WaskaLabs/40VA-SINGLE-MOSFET-SSTC/MINI SSTC 1 PICS/ARCS AND SPARKS 6.5 INCH 1.jpg

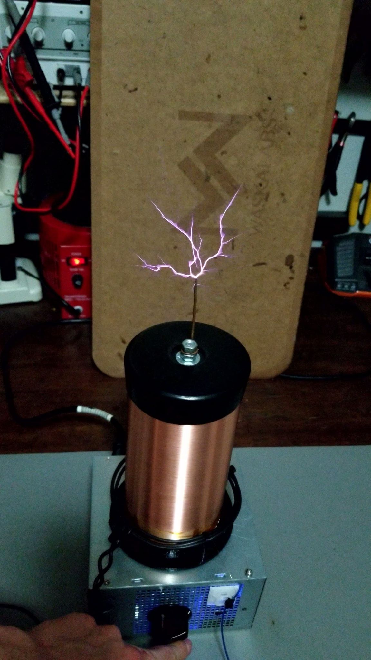
MINI SSTC 1 PICS/ARCS AND SPARKS 6.5 INCH 1.jpg
