WaskaLabs/40VA-SINGLE-MOSFET-SSTC/MINI SSTC 1 PICS/PCB PIC 1.jpg

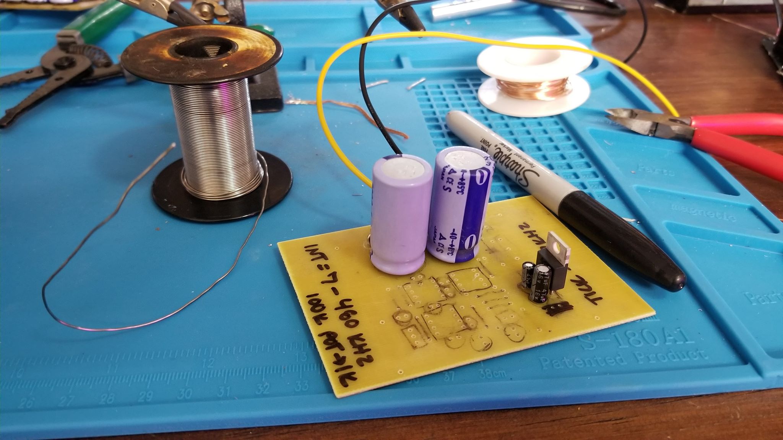
MINI SSTC 1 PICS/PCB PIC 1.jpg
