WaskaLabs/40VA-SINGLE-MOSFET-SSTC/V0 - MILLED VERSION/PCB & CONNECTIONS.png

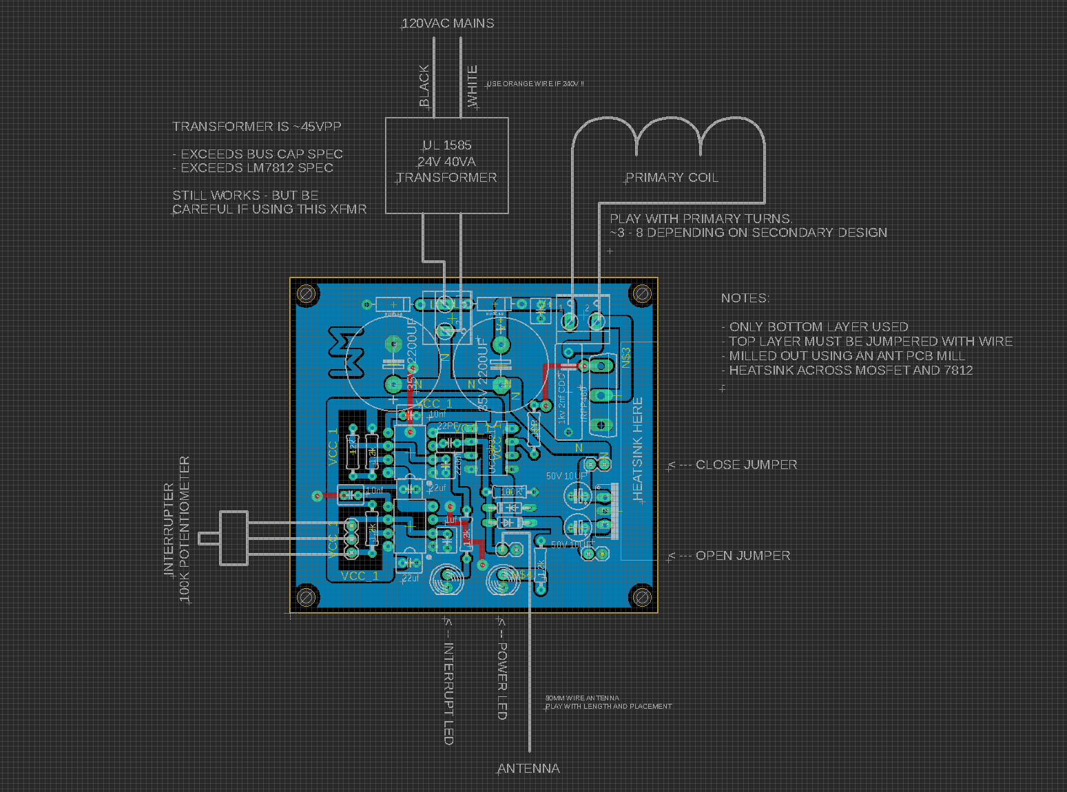
V0 - MILLED VERSION/PCB & CONNECTIONS.png
