WaskaLabs/40VA-SINGLE-MOSFET-SSTC/MINI SSTC 1 PICS/3D PRINTED COIL HOLDER.jpg

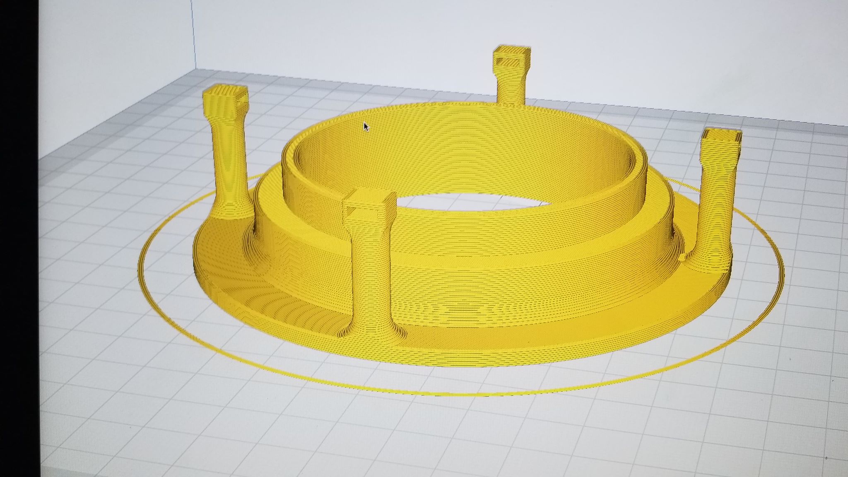
MINI SSTC 1 PICS/3D PRINTED COIL HOLDER.jpg
