WaskaLabs/40VA-SINGLE-MOSFET-SSTC/MINI SSTC 1 PICS/FINAL ASSEMBLY 4.jpg

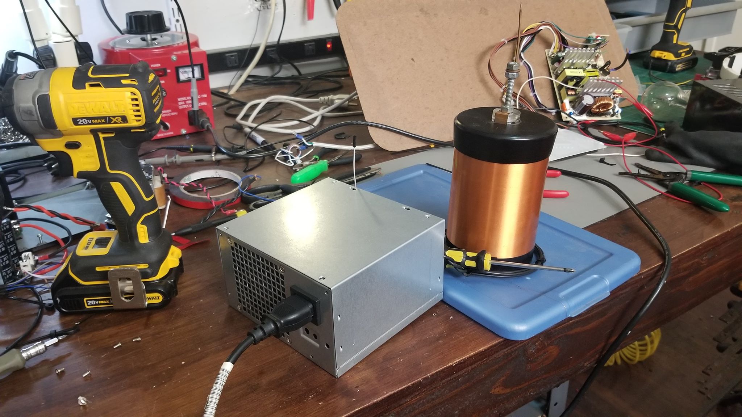
MINI SSTC 1 PICS/FINAL ASSEMBLY 4.jpg
