WaskaLabs/40VA-SINGLE-MOSFET-SSTC/MINI SSTC 1 PICS/FINAL ASSEMBLY 5.jpg

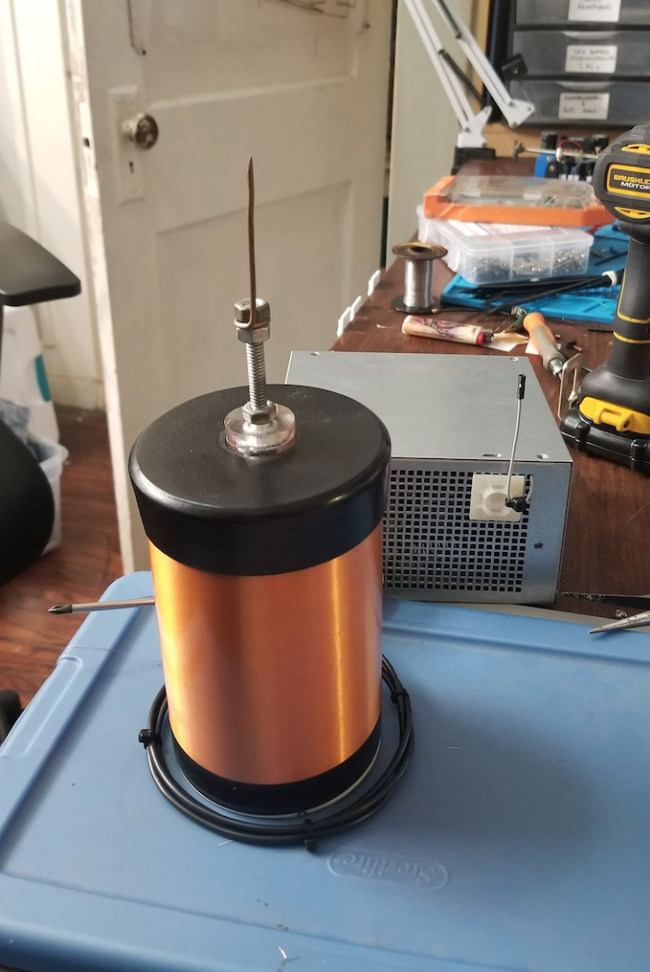
MINI SSTC 1 PICS/FINAL ASSEMBLY 5.jpg
