WaskaLabs/40VA-SINGLE-MOSFET-SSTC/MINI SSTC 1 PICS/FINAL ASSEMBLY GUTS.jpg

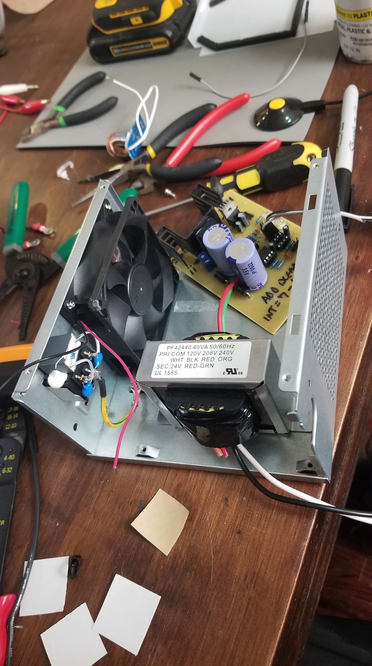
MINI SSTC 1 PICS/FINAL ASSEMBLY GUTS.jpg
