WaskaLabs/40VA-SINGLE-MOSFET-SSTC/MINI SSTC 1 PICS/FIRST PCB TESTS WITH 555 INTERRUPT.jpg

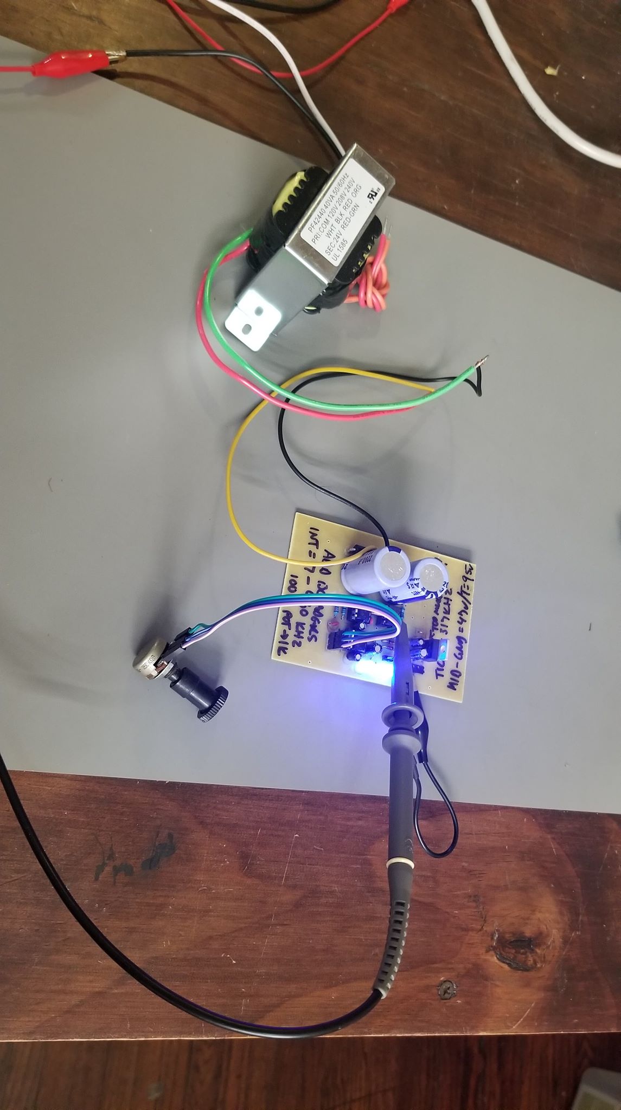
MINI SSTC 1 PICS/FIRST PCB TESTS WITH 555 INTERRUPT.jpg
